hacknus/open-source-ups/src/report.rs

//! HID report for 3-button mouse with a wheel.
//!
//! This example only uses one button and no wheel.
//! However we provided full report descriptor for
//! common mice so that one could easily reuse it.

use usbd_hid_device::HidReport;
use modular_bitfield::bitfield;
use modular_bitfield::prelude::*;
use modular_bitfield_to_value::ToValue;

pub const HID_PD_IPRODUCT: u8 = 0x01;               // FEATURE ONLY
pub const HID_PD_SERIAL: u8 = 0x02;                 // FEATURE ONLY
pub const HID_PD_MANUFACTURER: u8 = 0x03;           // FEATURE ONLY
pub const IDEVICECHEMISTRY: u8 = 0x04;
pub const IOEMVENDOR: u8 = 0x05;

pub const HID_PD_RECHARGEABLE: u8 = 0x06;           // FEATURE ONLY
pub const HID_PD_PRESENTSTATUS: u8 = 0x07;          // INPUT OR FEATURE(required by Windows)
pub const HID_PD_REMAINTIMELIMIT: u8 = 0x08;
pub const HID_PD_MANUFACTUREDATE: u8 = 0x09;
pub const HID_PD_CONFIGVOLTAGE: u8 = 0x0A;          // FEATURE ONLY
pub const HID_PD_VOLTAGE: u8 = 0x0B;                // INPUT (NA) OR FEATURE(implemented)
pub const HID_PD_REMAININGCAPACITY: u8 = 0x0C;      // INPUT OR FEATURE(required by Windows)
pub const HID_PD_RUNTIMETOEMPTY: u8 = 0x0D;
pub const HID_PD_FULLCHRGECAPACITY: u8 = 0x0E;      // INPUT OR FEATURE. Last Full Charge Capacity
pub const HID_PD_WARNCAPACITYLIMIT: u8 = 0x0F;
pub const HID_PD_CPCTYGRANULARITY1: u8 = 0x10;
pub const HID_PD_REMNCAPACITYLIMIT: u8 = 0x11;
pub const HID_PD_DELAYBE4SHUTDOWN: u8 = 0x12;       // FEATURE ONLY
pub const HID_PD_DELAYBE4REBOOT: u8 = 0x13;
pub const HID_PD_AUDIBLEALARMCTRL: u8 = 0x14;       // FEATURE ONLY
pub const HID_PD_CURRENT: u8 = 0x15;                // FEATURE ONLY
pub const HID_PD_CAPACITYMODE: u8 = 0x16;
pub const HID_PD_DESIGNCAPACITY: u8 = 0x17;
pub const HID_PD_CPCTYGRANULARITY2: u8 = 0x18;
pub const HID_PD_AVERAGETIME2FULL: u8 = 0x1A;
pub const HID_PD_AVERAGECURRENT: u8 = 0x1B;
pub const HID_PD_AVERAGETIME2EMPTY: u8 = 0x1C;

pub const HID_PD_IDEVICECHEMISTRY: u8 = 0x1F;       // Feature
pub const HID_PD_IOEMINFORMATION: u8 = 0x20;        // Feature

pub const IPRODUCT: u8 = 0x02;
pub const ISERIAL: u8 = 0x03;
pub const IMANUFACTURER: u8 = 0x01;

#[derive(Clone, Copy)]
#[allow(dead_code)]
#[bitfield(bits = 16)]
#[derive(ToValue)]
pub struct Status {
    pub charging: B1,
    pub discharging: B1,
    pub ac_present: B1,
    pub battery_present: B1,
    pub below_remaining_capacity_limit: B1,
    pub remaining_time_limit_expired: B1,
    pub need_replace: B1,
    pub voltage_nr: B1,
    pub full_charge: B1,
    pub full_discharge: B1,
    pub shutdown_requested: B1,
    pub shutdown_imminent: B1,
    pub communication_lost: B1,
    pub overload: B1,
    #[skip] _a: B2,
}

pub struct Report {
    pub bytes: [u8; 4],
}

impl Report {
    pub fn new_u8(id: u8, value: u8) -> Self {
        Report {
            bytes: [id, value, 8, 0],
        }
    }

    pub fn new_u16(id: u8, value: u16) -> Self {
        Report {
            bytes: [id, (value & 0xFF) as u8,(value >> 8) as u8, 16],
        }
    }

    pub fn update_u8_value(&mut self, value: u8) {
        self.bytes[1] = value;
    }

    pub fn update_u16_value(&mut self, value: u16) {
        self.bytes[1] = (value & 0xFF) as u8;
        self.bytes[2] = (value >> 8) as u8;
    }
}

impl AsRef<[u8]> for Report {
    fn as_ref(&self) -> &[u8] {
        &self.bytes
    }
}

impl HidReport for Report {
    const DESCRIPTOR: &'static [u8] = &[
        0x05, 0x84, // USAGE_PAGE (Power Device)
        0x09, 0x04, // USAGE (UPS)
        0xA1, 0x01, // COLLECTION (Application)
        0x09, 0x24, //   USAGE (Sink)
        0xA1, 0x02, //   COLLECTION (Logical)
        0x75, 0x08, //     REPORT_SIZE (8)
        0x95, 0x01, //     REPORT_COUNT (1)
        0x15, 0x00, //     LOGICAL_MINIMUM (0)
        0x26, 0xFF, 0x00, //     LOGICAL_MAXIMUM (255)
        0x85, HID_PD_IPRODUCT, //     REPORT_ID (1)
        0x09, 0xFE, //     USAGE (iProduct)
        0x79, IPRODUCT, //     STRING INDEX (2)
        0xB1, 0x23, //     FEATURE (Constant, Variable, Absolute, No Wrap, Linear, No Preferred, No Null Position, Nonvolatile, Bitfield)
        0x85, HID_PD_SERIAL, //     REPORT_ID (2)
        0x09, 0xFF, //     USAGE (iSerialNumber)
        0x79, ISERIAL, //  STRING INDEX (3)
        0xB1, 0x23, //     FEATURE (Constant, Variable, Absolute, No Wrap, Linear, No Preferred, No Null Position, Nonvolatile, Bitfield)
        0x85, HID_PD_MANUFACTURER, //     REPORT_ID (3)
        0x09, 0xFD, //     USAGE (iManufacturer)
        0x79, IMANUFACTURER, //     STRING INDEX (1)
        0xB1, 0x23, //     FEATURE (Constant, Variable, Absolute, No Wrap, Linear, No Preferred, No Null Position, Nonvolatile, Bitfield)
        0x05, 0x85, //     USAGE_PAGE (Battery System) ====================
        0x85, HID_PD_RECHARGEABLE, //     REPORT_ID (6)
        0x09, 0x8B, //     USAGE (Rechargable)
        0xB1, 0x23, //     FEATURE (Constant, Variable, Absolute, No Wrap, Linear, No Preferred, No Null Position, Nonvolatile, Bitfield)
        0x85, HID_PD_IDEVICECHEMISTRY, //     REPORT_ID (31)
        0x09, 0x89, //     USAGE (iDeviceChemistry)
        0x79, IDEVICECHEMISTRY, //     STRING INDEX (4)
        0xB1, 0x23, //     FEATURE (Constant, Variable, Absolute, No Wrap, Linear, No Preferred, No Null Position, Nonvolatile, Bitfield)
        0x85, HID_PD_IOEMINFORMATION,  //     REPORT_ID (32)
        0x09, 0x8F, //     USAGE (iOEMInformation)
        0x79, IOEMVENDOR, //     STRING INDEX (5)
        0xB1, 0x23, //     FEATURE (Constant, Variable, Absolute, No Wrap, Linear, No Preferred, No Null Position, Nonvolatile, Bitfield)
        0x85, HID_PD_CAPACITYMODE, //     REPORT_ID (22)
        0x09, 0x2C, //     USAGE (CapacityMode)
        0xB1, 0x23, //     FEATURE (Constant, Variable, Absolute, No Wrap, Linear, No Preferred, No Null Position, Nonvolatile, Bitfield)
        0x85, HID_PD_CPCTYGRANULARITY1, //     REPORT_ID (16)
        0x09, 0x8D, //     USAGE (CapacityGranularity1)
        0x26, 0x64, 0x00, //     LOGICAL_MAXIMUM (100)
        0xB1, 0x22, //     FEATURE (Data, Variable, Absolute, No Wrap, Linear, No Preferred, No Null Position, Nonvolatile, Bitfield)
        0x85, HID_PD_CPCTYGRANULARITY2, //     REPORT_ID (24)
        0x09, 0x8E, //     USAGE (CapacityGranularity2)
        0xB1, 0x23, //     FEATURE (Constant, Variable, Absolute, No Wrap, Linear, No Preferred, No Null Position, Nonvolatile, Bitfield)
        0x85, HID_PD_FULLCHRGECAPACITY, //     REPORT_ID (14)
        0x09, 0x67, //     USAGE (FullChargeCapacity)
        0xB1, 0x83, //     FEATURE (Constant, Variable, Absolute, No Wrap, Linear, No Preferred, No Null Position, Volatile, Bitfield)
        0x85, HID_PD_DESIGNCAPACITY, //     REPORT_ID (23)
        0x09, 0x83, //     USAGE (DesignCapacity)
        0xB1, 0x83, //     FEATURE (Constant, Variable, Absolute, No Wrap, Linear, No Preferred, No Null Position, Volatile, Bitfield)
        0x85, HID_PD_REMAININGCAPACITY, //     REPORT_ID (12)
        0x09, 0x66, //     USAGE (RemainingCapacity)
        0x81, 0xA3, //     INPUT (Constant, Variable, Absolute, No Wrap, Linear, No Preferred, No Null Position, Bitfield)
        0x09, 0x66, //     USAGE (RemainingCapacity)
        0xB1, 0xA3, //     FEATURE (Constant, Variable, Absolute, No Wrap, Linear, No Preferred, No Null Position, Volatile, Bitfield)
        0x85, HID_PD_WARNCAPACITYLIMIT, //     REPORT_ID (15)
        0x09, 0x8C, //     USAGE (WarningCapacityLimit)
        0xB1, 0xA2, //     FEATURE (Data, Variable, Absolute, No Wrap, Linear, No Preferred, No Null Position, Volatile, Bitfield)
        0x85, HID_PD_REMNCAPACITYLIMIT, //     REPORT_ID (17)
        0x09, 0x29, //     USAGE (RemainingCapacityLimit)
        0xB1, 0xA2, //     FEATURE (Data, Variable, Absolute, No Wrap, Linear, No Preferred, No Null Position, Volatile, Bitfield)
        0x85, HID_PD_MANUFACTUREDATE, //     REPORT_ID (9)
        0x09, 0x85, //     USAGE (ManufacturerDate)
        0x75, 0x10, //     REPORT_SIZE (16)
        0x27, 0xFF, 0xFF, 0x00, 0x00, //     LOGICAL_MAXIMUM (65534)
        0xB1, 0xA3, //     FEATURE (Constant, Variable, Absolute, No Wrap, Linear, No Preferred, No Null Position, Volatile, Bitfield)
        0x85, HID_PD_AVERAGETIME2FULL, //     REPORT_ID (26)
        0x09, 0x6A, //     USAGE (AverageTimeToFull)
        0x27, 0xFF, 0xFF, 0x00, 0x00, //     LOGICAL_MAXIMUM (65534)
        0x66, 0x01, 0x10, //     UNIT (Seconds)
        0x55, 0x00, //     UNIT_EXPONENT (0)
        0xB1, 0xA3, //     FEATURE (Constant, Variable, Absolute, No Wrap, Linear, No Preferred, No Null Position, Volatile, Bitfield)
        0x85, HID_PD_AVERAGETIME2EMPTY, //     REPORT_ID (28)
        0x09, 0x69, //     USAGE (AverageTimeToEmpty)
        0x81, 0xA3, //     INPUT (Constant, Variable, Absolute, No Wrap, Linear, No Preferred, No Null Position, Bitfield)
        0x09, 0x69, //     USAGE (AverageTimeToEmpty)
        0xB1, 0xA3, //     FEATURE (Constant, Variable, Absolute, No Wrap, Linear, No Preferred, No Null Position, Volatile, Bitfield)
        0x85, HID_PD_RUNTIMETOEMPTY, //     REPORT_ID (13)
        0x09, 0x68, //     USAGE (RunTimeToEmpty)
        0x81, 0xA3, //     INPUT (Constant, Variable, Absolute, No Wrap, Linear, No Preferred, No Null Position, Bitfield)
        0x09, 0x68, //     USAGE (RunTimeToEmpty)
        0xB1, 0xA3, //     FEATURE (Constant, Variable, Absolute, No Wrap, Linear, No Preferred, No Null Position, Volatile, Bitfield)
        0x85, HID_PD_REMAINTIMELIMIT, //     REPORT_ID (8)
        0x09, 0x2A, //     USAGE (RemainingTimeLimit)
        0x75, 0x10, //     REPORT_SIZE (16)
        0x27, 0x64, 0x05, 0x00, 0x00, //     LOGICAL_MAXIMUM (1380)
        0x16, 0x78, 0x00, //     LOGICAL_MINIMUM (120)
        0x81, 0x22, //     INPUT (Data, Variable, Absolute, No Wrap, Linear, No Preferred, No Null Position, Bitfield)
        0x09, 0x2A, //     USAGE (RemainingTimeLimit)
        0xB1, 0xA2, //     FEATURE (Data, Variable, Absolute, No Wrap, Linear, No Preferred, No Null Position, Volatile, Bitfield)
        0x05, 0x84, //     USAGE_PAGE (Power Device) ====================
        0x85, HID_PD_DELAYBE4SHUTDOWN, //     REPORT_ID (18)
        0x09, 0x57, //     USAGE (DelayBeforeShutdown)
        0x16, 0x00, 0x80, //     LOGICAL_MINIMUM (-32768)
        0x27, 0xFF, 0x7F, 0x00, 0x00, //     LOGICAL_MAXIMUM (32767)
        0xB1, 0xA2, //     FEATURE (Data, Variable, Absolute, No Wrap, Linear, No Preferred, No Null Position, Volatile, Bitfield)
        0x85, HID_PD_DELAYBE4REBOOT, //     REPORT_ID (19)
        0x09, 0x55, //     USAGE (DelayBeforeReboot)
        0xB1, 0xA2, //     FEATURE (Data, Variable, Absolute, No Wrap, Linear, No Preferred, No Null Position, Volatile, Bitfield)
        0x85, HID_PD_CONFIGVOLTAGE, //     REPORT_ID (10)
        0x09, 0x40, //     USAGE (ConfigVoltage)
        0x15, 0x00, //     LOGICAL_MINIMUM (0)
        0x27, 0xFF, 0xFF, 0x00, 0x00, //     LOGICAL_MAXIMUM (65535)
        0x67, 0x21, 0xD1, 0xF0, 0x00, //     UNIT (Centivolts)
        0x55, 0x05, //     UNIT_EXPONENT (5)
        0xB1, 0x23, //     FEATURE (Constant, Variable, Absolute, No Wrap, Linear, No Preferred, No Null Position, Nonvolatile, Bitfield)
        0x85, HID_PD_VOLTAGE, //     REPORT_ID (11)
        0x09, 0x30, //     USAGE (Voltage)
        0x81, 0xA3, //     INPUT (Constant, Variable, Absolute, No Wrap, Linear, No Preferred, No Null Position, Bitfield)
        0x09, 0x30, //     USAGE (Voltage)
        0xB1, 0xA3, //     FEATURE (Constant, Variable, Absolute, No Wrap, Linear, No Preferred, No Null Position, Volatile, Bitfield)
        0x85, HID_PD_AUDIBLEALARMCTRL, //     REPORT_ID (20)
        0x09, 0x5A, //     USAGE (AudibleAlarmControl)
        0x75, 0x08, //     REPORT_SIZE (8)
        0x15, 0x01, //     LOGICAL_MINIMUM (1)
        0x25, 0x03, //     LOGICAL_MAXIMUM (3)
        0x65, 0x00, //     UNIT (0)
        0x55, 0x00, //     UNIT_EXPONENT (0)
        0x81, 0x22, //     INPUT (Data, Variable, Absolute, No Wrap, Linear, No Preferred, No Null Position, Bitfield)
        0x09, 0x5A, //     USAGE (AudibleAlarmControl)
        0xB1, 0xA2, //     FEATURE (Data, Variable, Absolute, No Wrap, Linear, No Preferred, No Null Position, Volatile, Bitfield)
        0x09, 0x02, //     USAGE (PresentStatus)
        0xA1, 0x02, //     COLLECTION (Logical)
        0x85, HID_PD_PRESENTSTATUS, //       REPORT_ID (7)
        0x05, 0x85, //       USAGE_PAGE (Battery System) =================
        0x09, 0x44, //       USAGE (Charging)
        0x75, 0x01, //       REPORT_SIZE (1)
        0x15, 0x00, //       LOGICAL_MINIMUM (0)
        0x25, 0x01, //       LOGICAL_MAXIMUM (1)
        0x81, 0xA3, //       INPUT (Constant, Variable, Absolute, No Wrap, Linear, No Preferred, No Null Position, Bitfield)
        0x09, 0x44, //       USAGE (Charging)
        0xB1, 0xA3, //       FEATURE (Constant, Variable, Absolute, No Wrap, Linear, No Preferred, No Null Position, Volatile, Bitfield)
        0x09, 0x45, //       USAGE (Discharging)
        0x81, 0xA3, //       INPUT (Constant, Variable, Absolute, No Wrap, Linear, No Preferred, No Null Position, Bitfield)
        0x09, 0x45, //       USAGE (Discharging)
        0xB1, 0xA3, //       FEATURE (Constant, Variable, Absolute, No Wrap, Linear, No Preferred, No Null Position, Volatile, Bitfield)
        0x09, 0xD0, //       USAGE (ACPresent)
        0x81, 0xA3, //       INPUT (Constant, Variable, Absolute, No Wrap, Linear, No Preferred, No Null Position, Bitfield)
        0x09, 0xD0, //       USAGE (ACPresent)
        0xB1, 0xA3, //       FEATURE (Constant, Variable, Absolute, No Wrap, Linear, No Preferred, No Null Position, Volatile, Bitfield)
        0x09, 0xD1, //       USAGE (BatteryPresent)
        0x81, 0xA3, //       INPUT (Constant, Variable, Absolute, No Wrap, Linear, No Preferred, No Null Position, Bitfield)
        0x09, 0xD1, //       USAGE (BatteryPresent)
        0xB1, 0xA3, //       FEATURE (Constant, Variable, Absolute, No Wrap, Linear, No Preferred, No Null Position, Volatile, Bitfield)
        0x09, 0x42, //       USAGE (BelowRemainingCapacityLimit)
        0x81, 0xA3, //       INPUT (Constant, Variable, Absolute, No Wrap, Linear, No Preferred, No Null Position, Bitfield)
        0x09, 0x42, //       USAGE (BelowRemainingCapacityLimit)
        0xB1, 0xA3, //       FEATURE (Constant, Variable, Absolute, No Wrap, Linear, No Preferred, No Null Position, Volatile, Bitfield)
        0x09, 0x43, //       USAGE (RemainingTimeLimitExpired)
        0x81, 0xA2, //       INPUT (Data, Variable, Absolute, No Wrap, Linear, No Preferred, No Null Position, Bitfield)
        0x09, 0x43, //       USAGE (RemainingTimeLimitExpired)
        0xB1, 0xA2, //       FEATURE (Data, Variable, Absolute, No Wrap, Linear, No Preferred, No Null Position, Volatile, Bitfield)
        0x09, 0x4B, //       USAGE (NeedReplacement)
        0x81, 0xA3, //       INPUT (Constant, Variable, Absolute, No Wrap, Linear, No Preferred, No Null Position, Bitfield)
        0x09, 0x4B, //       USAGE (NeedReplacement)
        0xB1, 0xA3, //       FEATURE (Constant, Variable, Absolute, No Wrap, Linear, No Preferred, No Null Position, Volatile, Bitfield)
        0x09, 0xDB, //       USAGE (VoltageNotRegulated)
        0x81, 0xA3, //       INPUT (Constant, Variable, Absolute, No Wrap, Linear, No Preferred, No Null Position, Bitfield)
        0x09, 0xDB, //       USAGE (VoltageNotRegulated)
        0xB1, 0xA3, //       FEATURE (Constant, Variable, Absolute, No Wrap, Linear, No Preferred, No Null Position, Volatile, Bitfield)
        0x09, 0x46, //       USAGE (FullyCharged)
        0x81, 0xA3, //       INPUT (Constant, Variable, Absolute, No Wrap, Linear, No Preferred, No Null Position, Bitfield)
        0x09, 0x46, //       USAGE (FullyCharged)
        0xB1, 0xA3, //       FEATURE (Constant, Variable, Absolute, No Wrap, Linear, No Preferred, No Null Position, Volatile, Bitfield)
        0x09, 0x47, //       USAGE (FullyDischarged)
        0x81, 0xA3, //       INPUT (Constant, Variable, Absolute, No Wrap, Linear, No Preferred, No Null Position, Bitfield)
        0x09, 0x47, //       USAGE (FullyDischarged)
        0xB1, 0xA3, //       FEATURE (Constant, Variable, Absolute, No Wrap, Linear, No Preferred, No Null Position, Volatile, Bitfield)
        0x05, 0x84, //       USAGE_PAGE (Power Device) =================
        0x09, 0x68, //       USAGE (ShutdownRequested)
        0x81, 0xA2, //       INPUT (Data, Variable, Absolute, No Wrap, Linear, No Preferred, No Null Position, Bitfield)
        0x09, 0x68, //       USAGE (ShutdownRequested)
        0xB1, 0xA2, //       FEATURE (Data, Variable, Absolute, No Wrap, Linear, No Preferred, No Null Position, Volatile, Bitfield)
        0x09, 0x69, //       USAGE (ShutdownImminent)
        0x81, 0xA3, //       INPUT (Constant, Variable, Absolute, No Wrap, Linear, No Preferred, No Null Position, Bitfield)
        0x09, 0x69, //       USAGE (ShutdownImminent)
        0xB1, 0xA3, //       FEATURE (Constant, Variable, Absolute, No Wrap, Linear, No Preferred, No Null Position, Volatile, Bitfield)
        0x09, 0x73, //       USAGE (CommunicationLost)
        0x81, 0xA3, //       INPUT (Constant, Variable, Absolute, No Wrap, Linear, No Preferred, No Null Position, Bitfield)
        0x09, 0x73, //       USAGE (CommunicationLost)
        0xB1, 0xA3, //       FEATURE (Constant, Variable, Absolute, No Wrap, Linear, No Preferred, No Null Position, Volatile, Bitfield)
        0x09, 0x65, //       USAGE (Overload)
        0x81, 0xA3, //       INPUT (Constant, Variable, Absolute, No Wrap, Linear, No Preferred, No Null Position, Bitfield)
        0x09, 0x65, //       USAGE (Overload)
        0xB1, 0xA3, //       FEATURE (Constant, Variable, Absolute, No Wrap, Linear, No Preferred, No Null Position, Volatile, Bitfield)
        0x95, 0x02, //       REPORT_COUNT (2)
        0x81, 0x01, //       INPUT (Constant, Array, Absolute)
        0xB1, 0x01, //       FEATURE (Constant, Array, Absolute, No Wrap, Linear, Preferred State, No Null Position, Nonvolatile, Bitfield)
        0xC0,       //     END_COLLECTION
        0xC0,       //   END_COLLECTION
        0xC0        // END_COLLECTION
    ];
}
